blueOkiris/FightKey/pico/src/report.c

#include <tusb.h>

/*
 * Invoked when received GET_REPORT control request
 * Application must fill buffer report's content and return its length.
 * Return zero will cause the stack to STALL request
 */
uint16_t tud_hid_get_report_cb(
        uint8_t instance,
        uint8_t report_id, hid_report_type_t report_type,
        uint8_t *buffer, uint16_t reqlen) {
    // TODO not Implemented
    (void) report_id;
    (void) report_type;
    (void) buffer;
    (void) reqlen;

    return 0;
}

/*
 * Invoked when received SET_REPORT control request or
 * received data on OUT endpoint ( Report ID = 0, Type = 0 )
 */
void tud_hid_set_report_cb(
        uint8_t instance,
        uint8_t report_id, hid_report_type_t report_type,
        uint8_t const *buffer, uint16_t bufsize) {
    // TODO set LED based on CAPLOCK, NUMLOCK etc...
    (void) report_id;
    (void) report_type;
    (void) buffer;
    (void) bufsize;
}
